drmoratorius/holmes-o-matic/docs/8 crime images/breakin.png

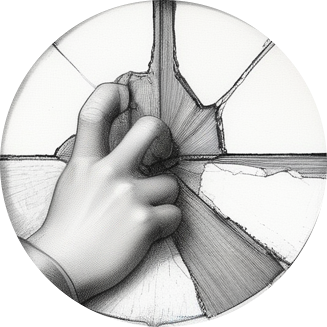
docs/8 crime images/breakin.png
