drmoratorius/holmes-o-matic/docs/8 crime images/cross.png

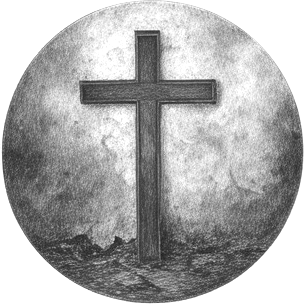
docs/8 crime images/cross.png
