drmoratorius/holmes-o-matic/docs/8 crime images/money.png

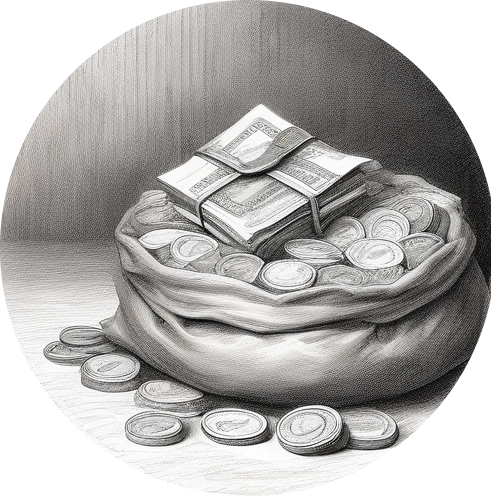
docs/8 crime images/money.png
